davidtcalabrese/ISWAM/embedded/HW/LevelShifter.png

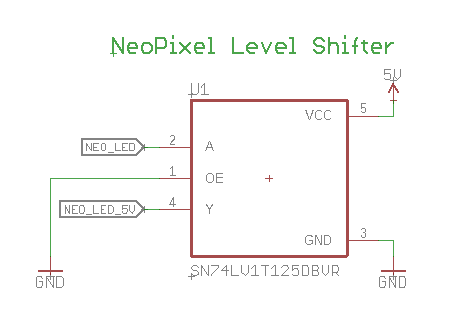
embedded/HW/LevelShifter.png
