davidtcalabrese/ISWAM/embedded/images/PXL_20211130_035253407.jpg

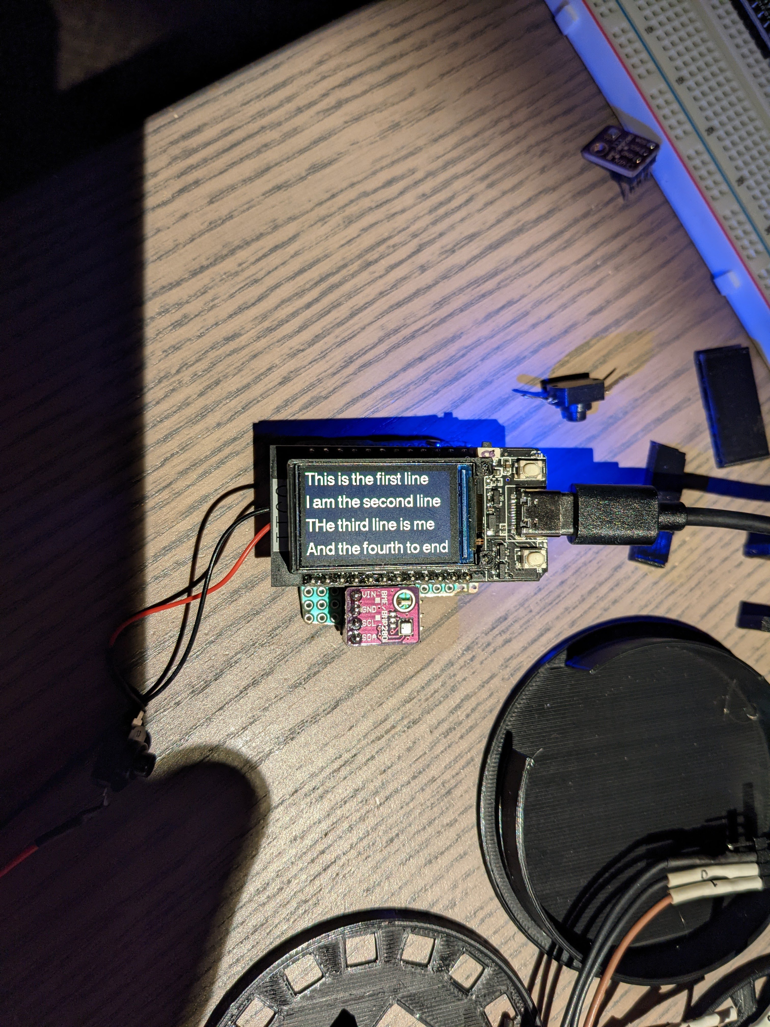
embedded/images/PXL_20211130_035253407.jpg
