davidtcalabrese/ISWAM/embedded/images/PXL_20211130_214545784.jpg

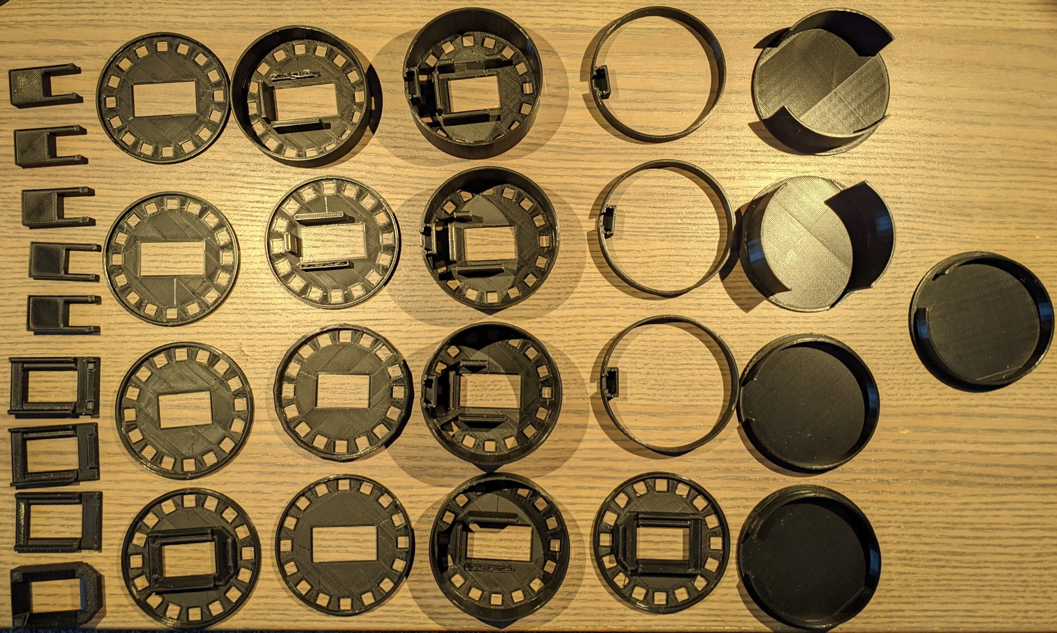
embedded/images/PXL_20211130_214545784.jpg
