davidtcalabrese/ISWAM/embedded/images/PXL_20211130_220826384.jpg

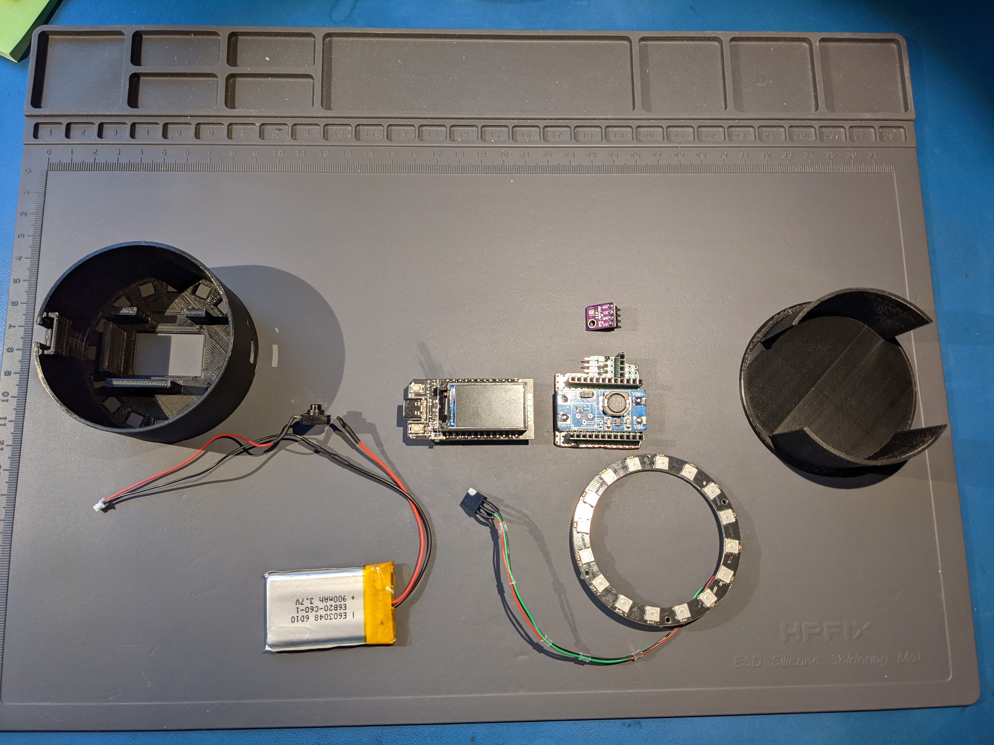
embedded/images/PXL_20211130_220826384.jpg
