davidtcalabrese/ISWAM/embedded/images/PXL_20211130_220832850.jpg

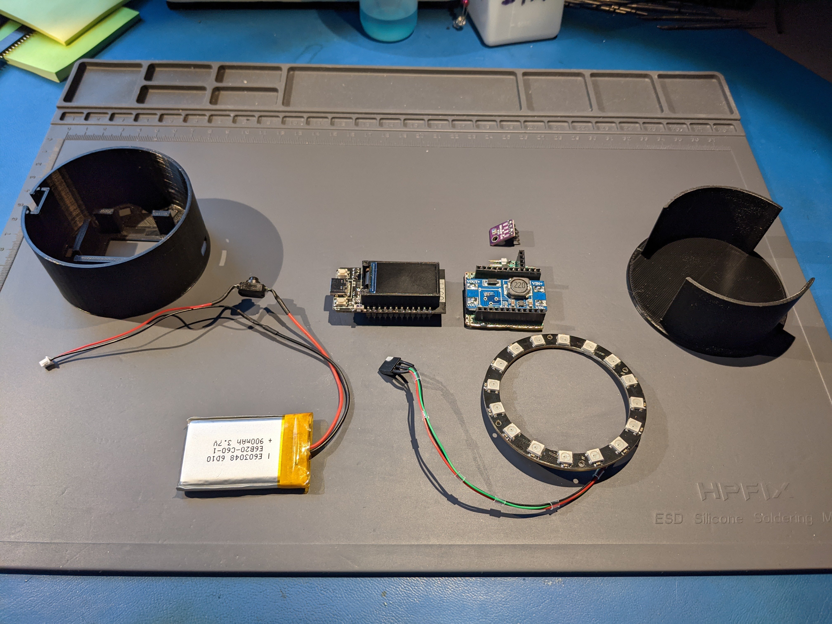
embedded/images/PXL_20211130_220832850.jpg
