davidtcalabrese/ISWAM/embedded/images/PXL_20211130_220852497.jpg

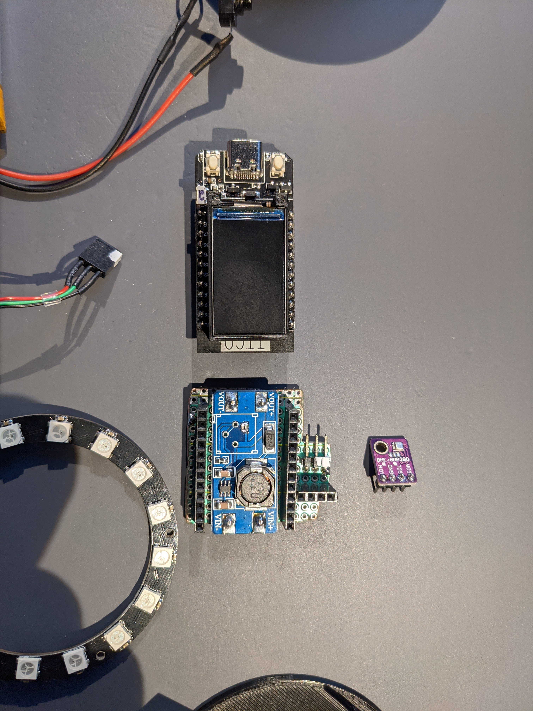
embedded/images/PXL_20211130_220852497.jpg
