davidtcalabrese/ISWAM/embedded/images/PXL_20211130_220959942.jpg

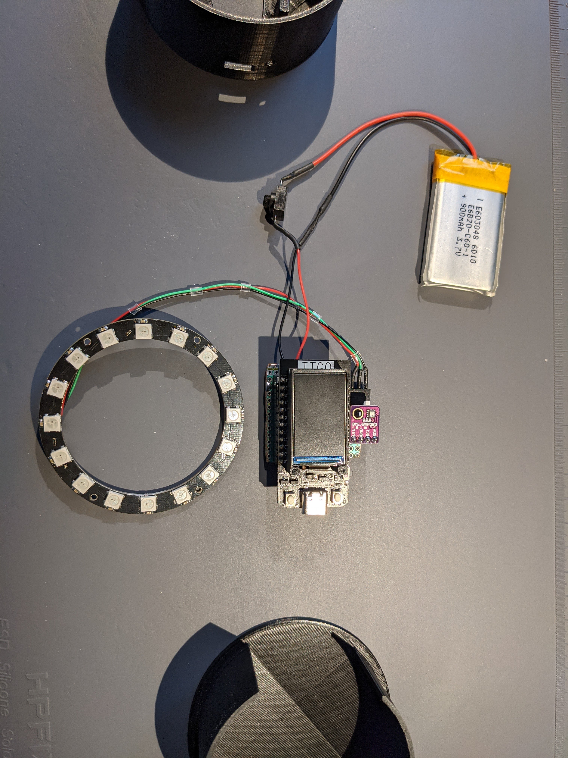
embedded/images/PXL_20211130_220959942.jpg
