davidtcalabrese/ISWAM/embedded/images/PXL_20211130_221004444.jpg

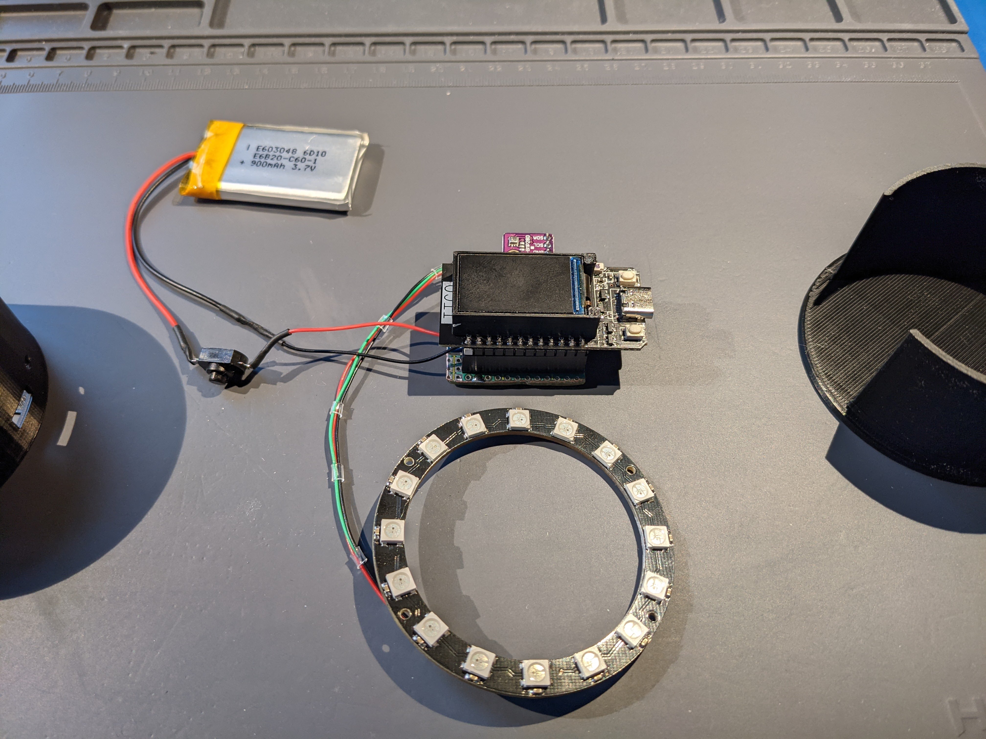
embedded/images/PXL_20211130_221004444.jpg
