davidtcalabrese/ISWAM/embedded/images/PXL_20211130_221025446.jpg

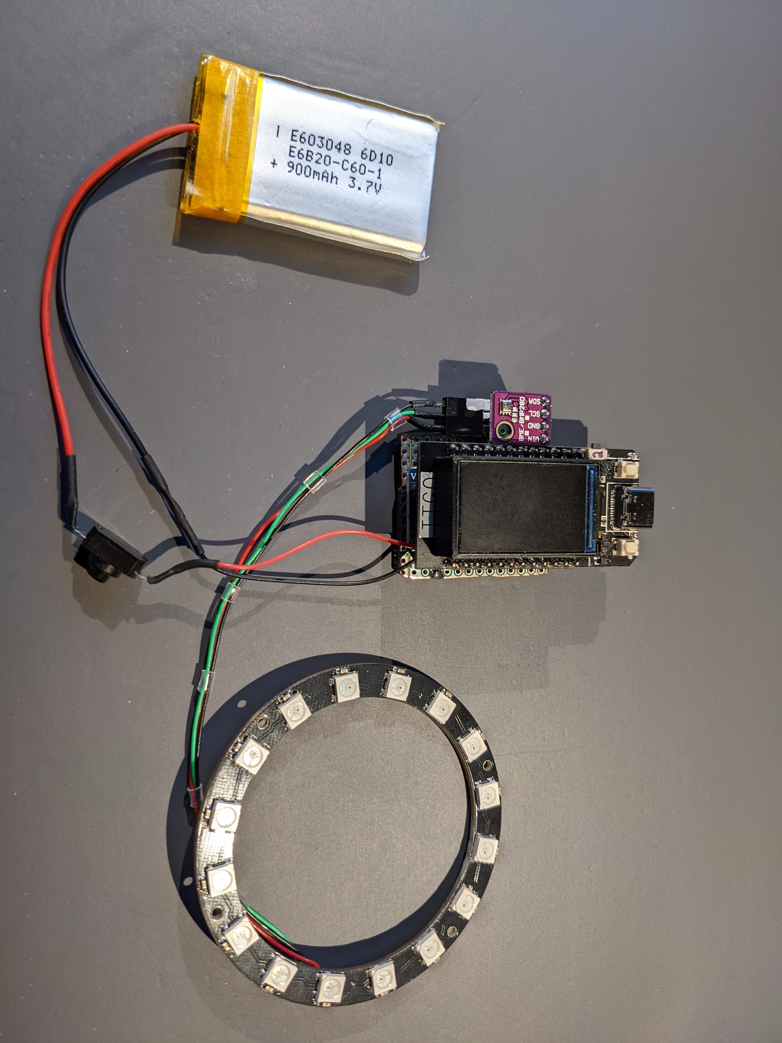
embedded/images/PXL_20211130_221025446.jpg
