davidtcalabrese/ISWAM/embedded/images/PXL_20211130_221055583.jpg

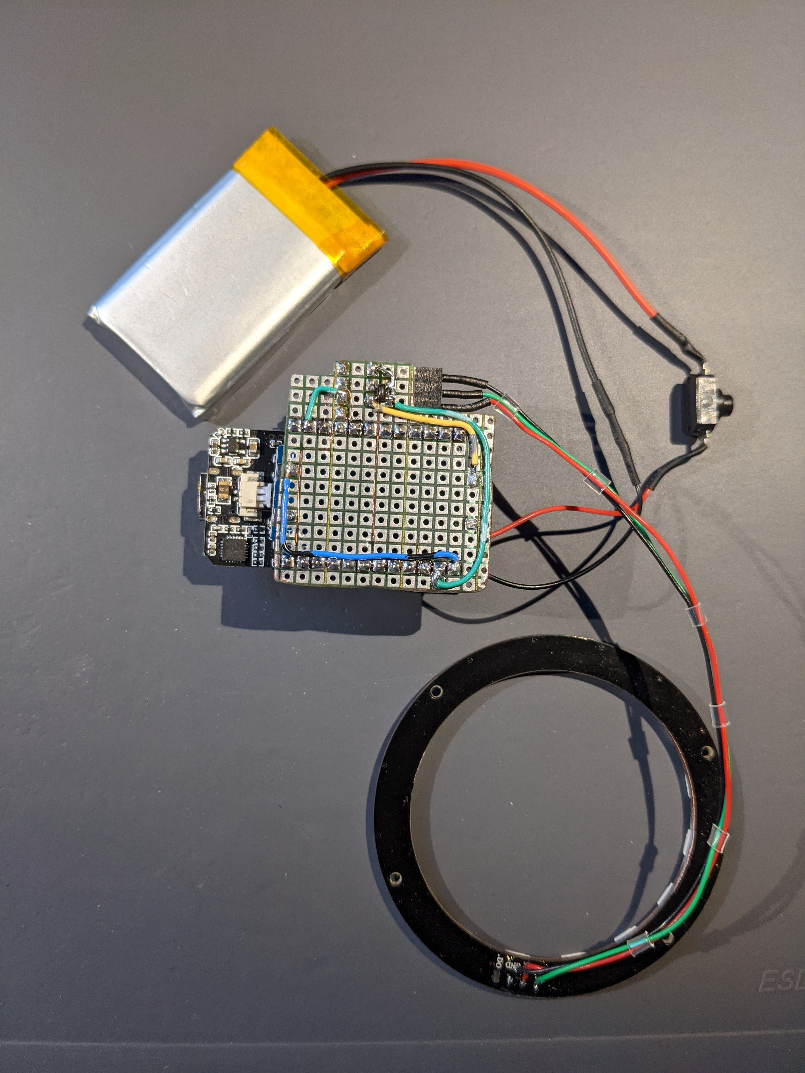
embedded/images/PXL_20211130_221055583.jpg
