davidtcalabrese/ISWAM/embedded/images/PXL_20211130_221106135.jpg

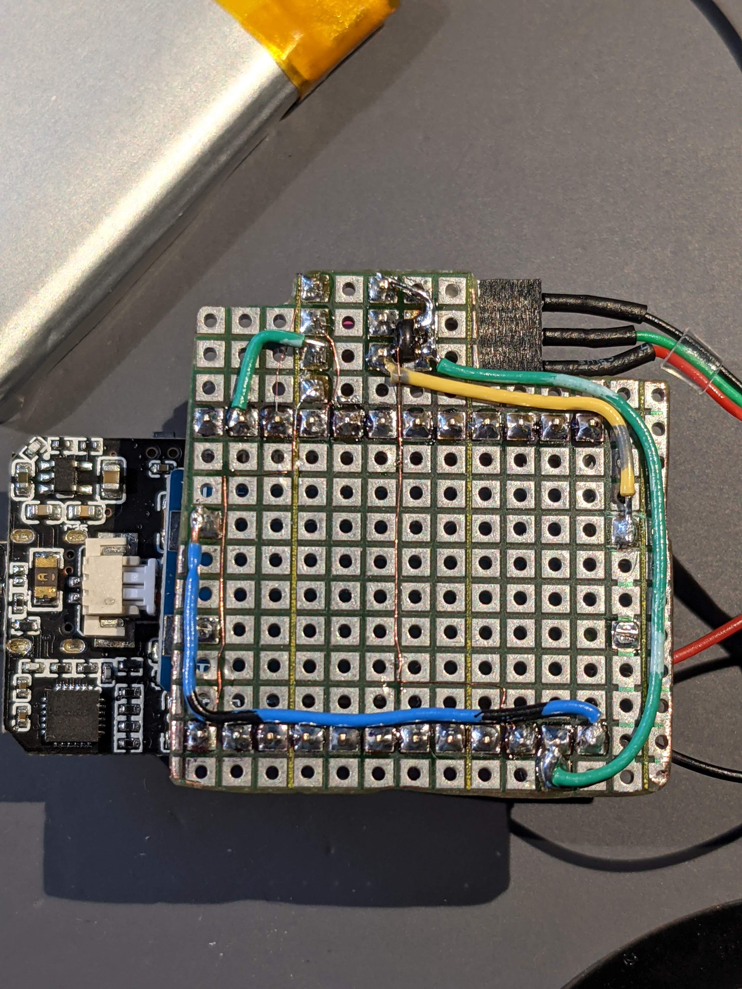
embedded/images/PXL_20211130_221106135.jpg
