davidtcalabrese/ISWAM/embedded/images/PXL_20211130_223039341.jpg

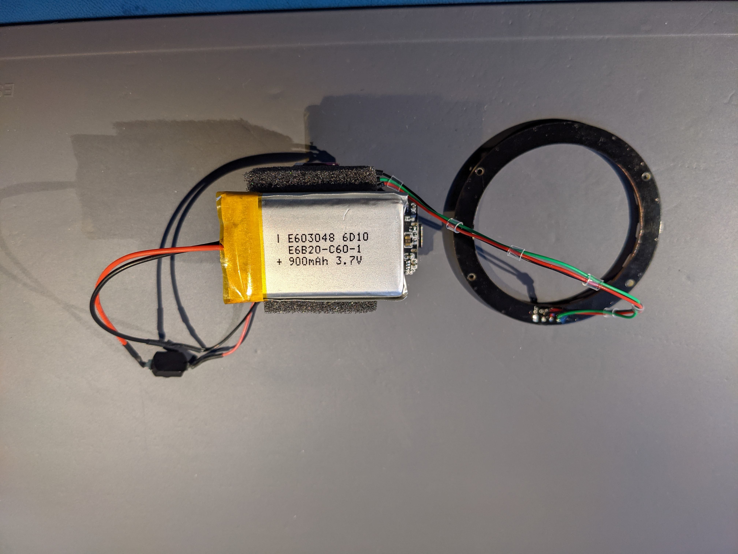
embedded/images/PXL_20211130_223039341.jpg
