davidtcalabrese/ISWAM/embedded/images/PXL_20211130_223052004.jpg

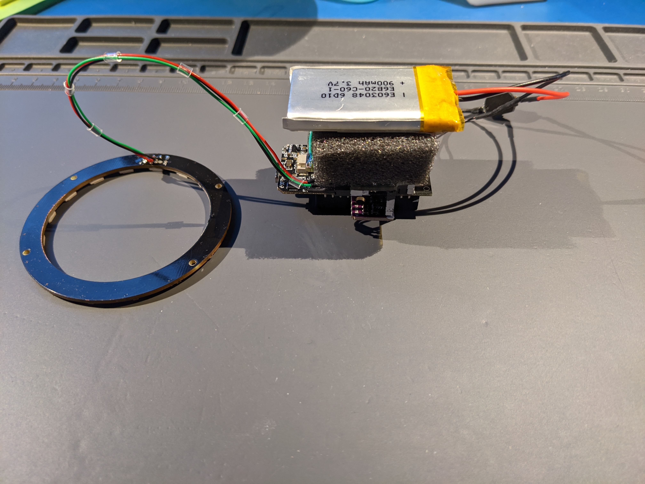
embedded/images/PXL_20211130_223052004.jpg
