davidtcalabrese/ISWAM/embedded/images/PXL_20211130_223111484.jpg

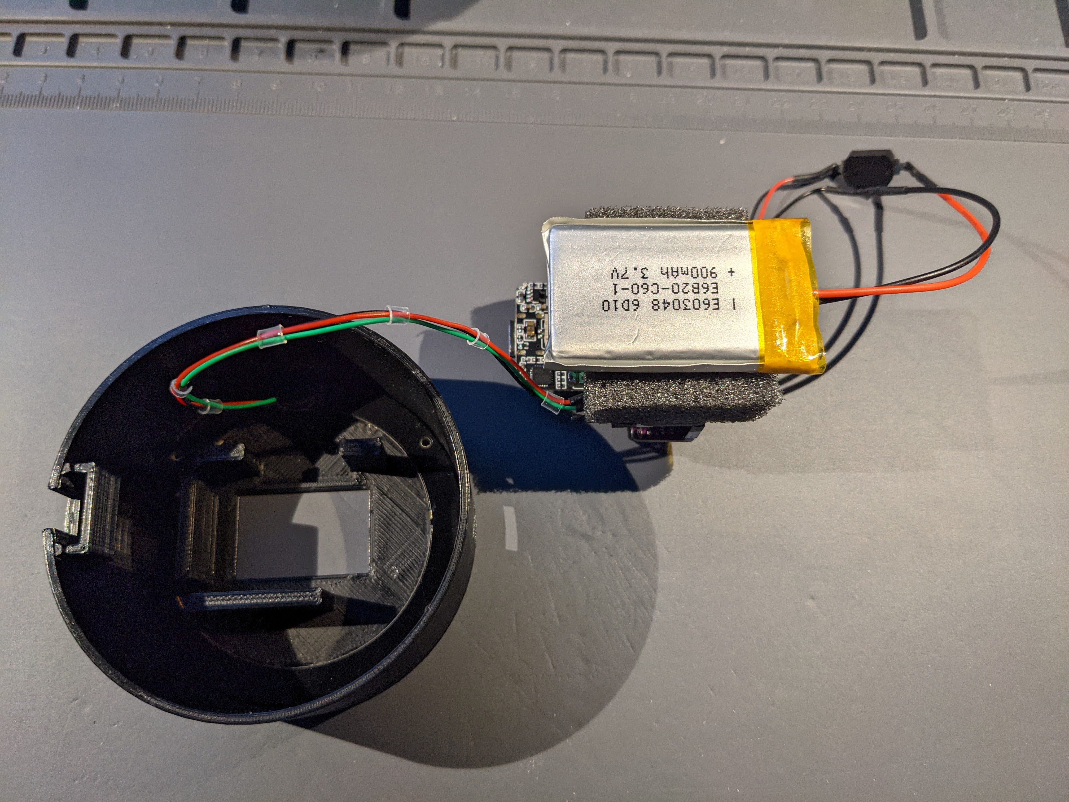
embedded/images/PXL_20211130_223111484.jpg
