davidtcalabrese/ISWAM/embedded/images/PXL_20211130_223149158.jpg

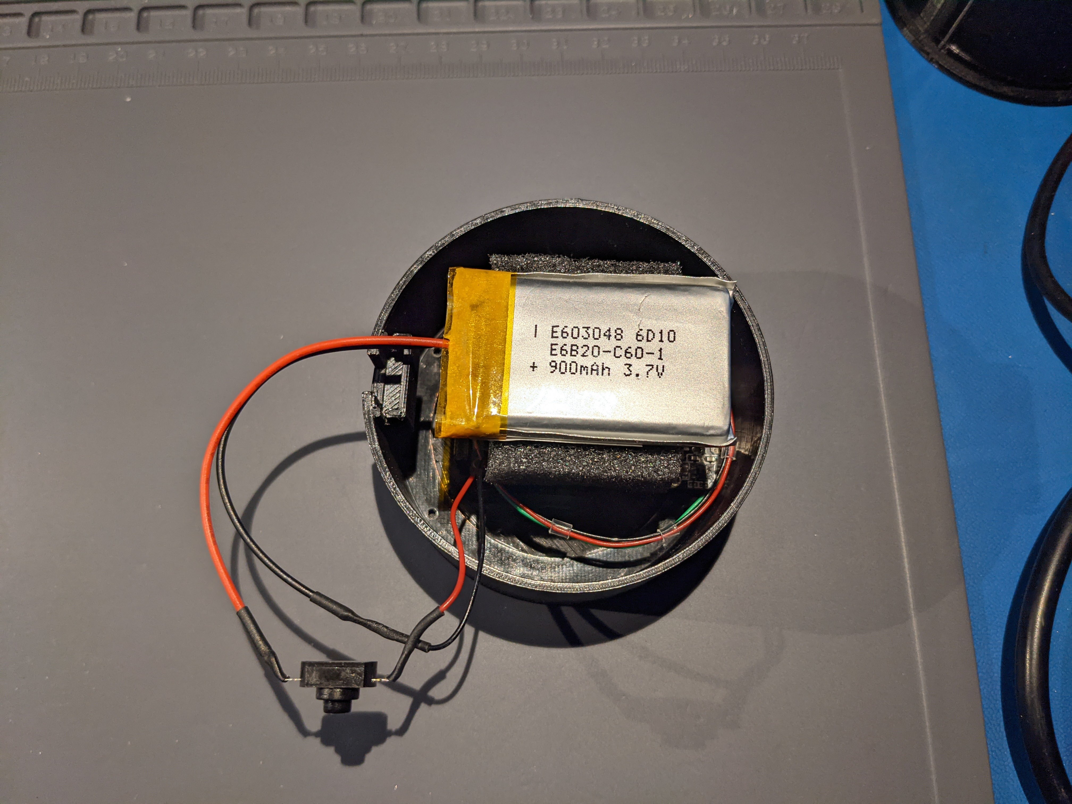
embedded/images/PXL_20211130_223149158.jpg
