davidtcalabrese/ISWAM/embedded/images/PXL_20211130_223400351.jpg

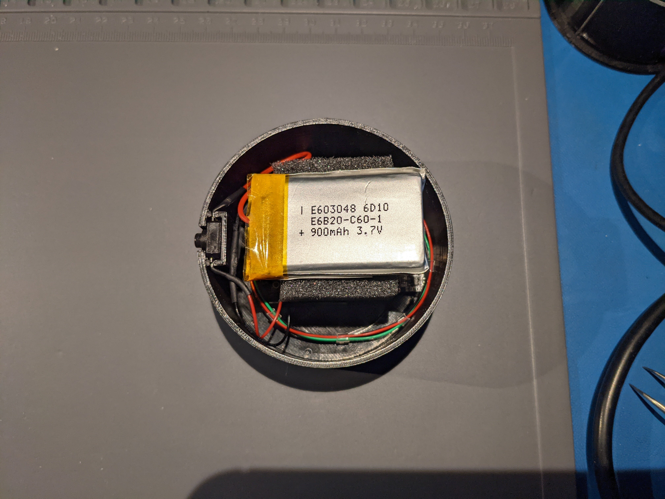
embedded/images/PXL_20211130_223400351.jpg
