davidtcalabrese/ISWAM/embedded/images/PXL_20211130_223430820.jpg

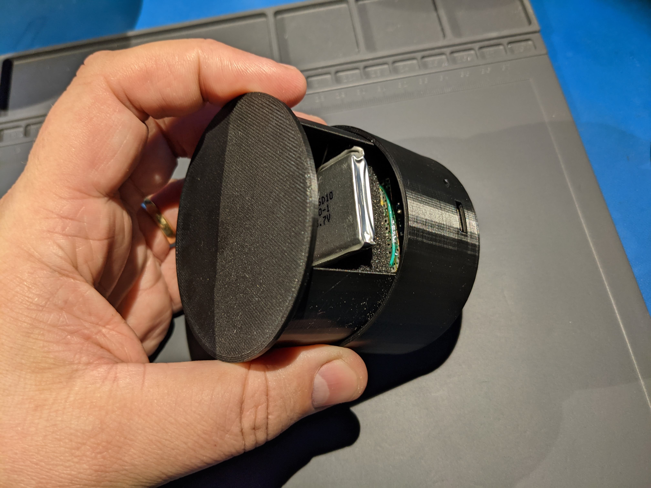
embedded/images/PXL_20211130_223430820.jpg
