davidtcalabrese/ISWAM/embedded/images/PXL_20211130_223858507.jpg

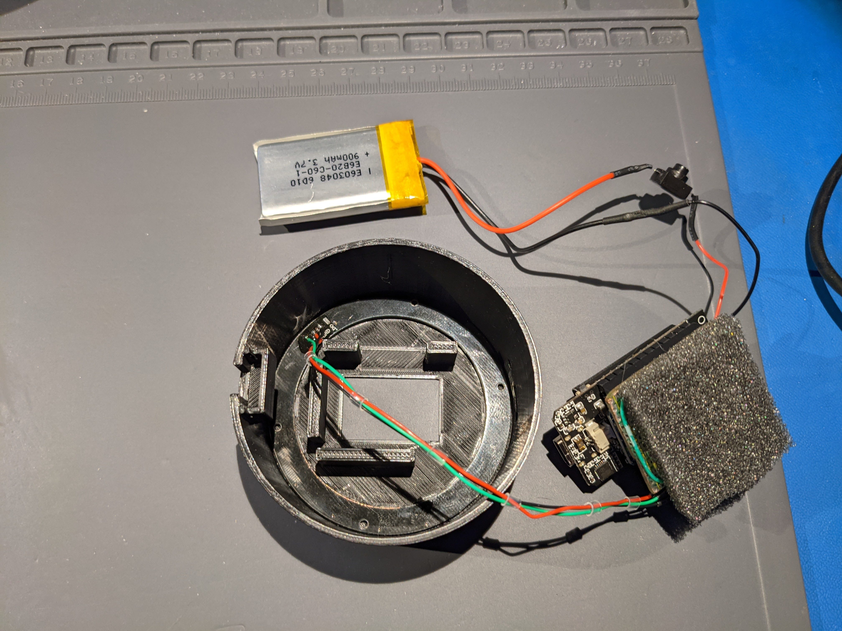
embedded/images/PXL_20211130_223858507.jpg
