davidtcalabrese/ISWAM/embedded/images/PXL_20211130_223935973.jpg

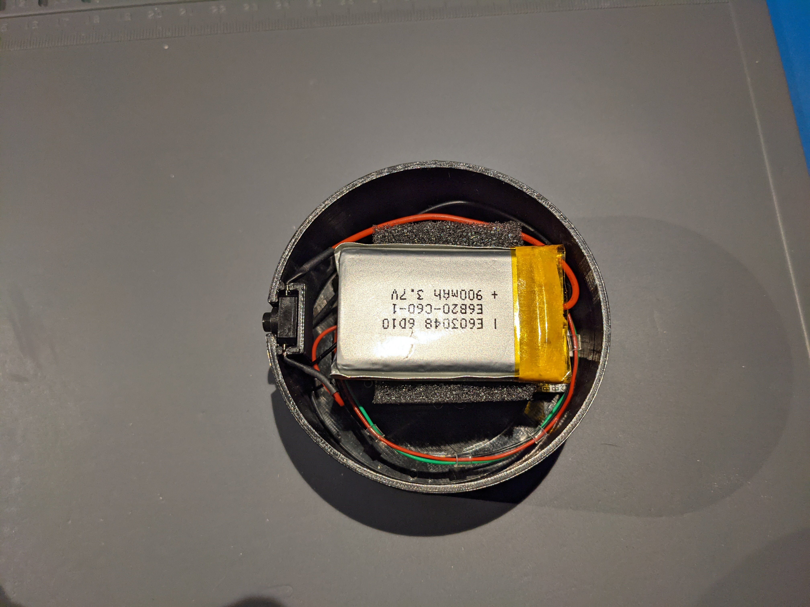
embedded/images/PXL_20211130_223935973.jpg
